johnyHV/SolderDispenser/FOTO/P_20200408_205617.jpg

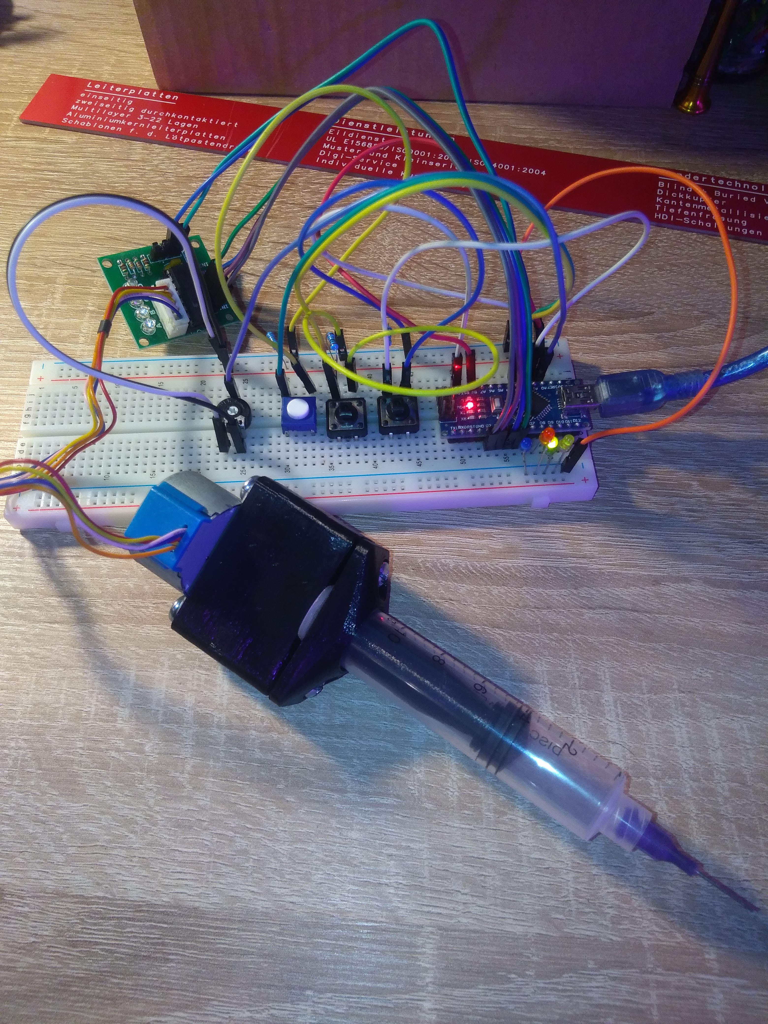
FOTO/P_20200408_205617.jpg
