johnyHV/SolderDispenser/FOTO/P_20200415_191209.jpg

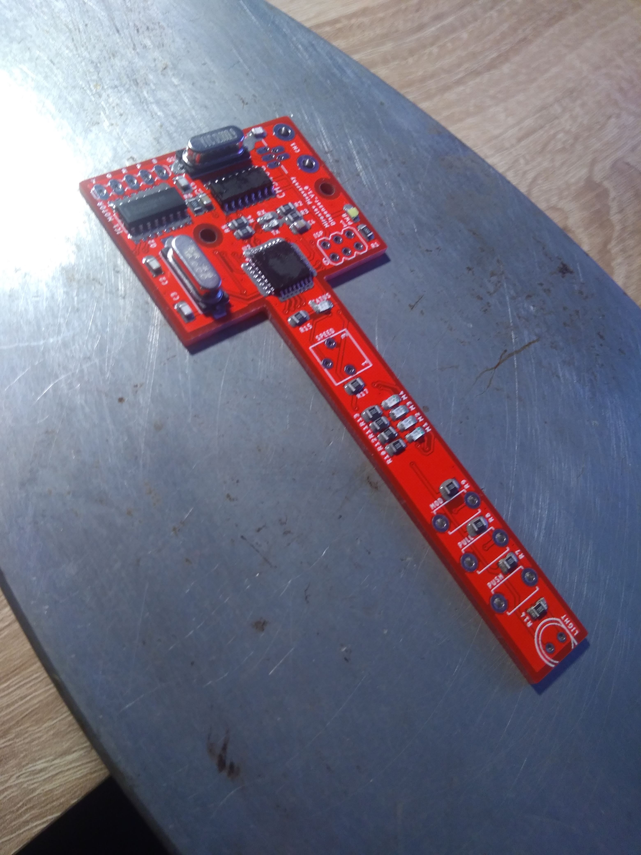
FOTO/P_20200415_191209.jpg
