johnyHV/SolderDispenser/FOTO/P_20200415_212830.jpg

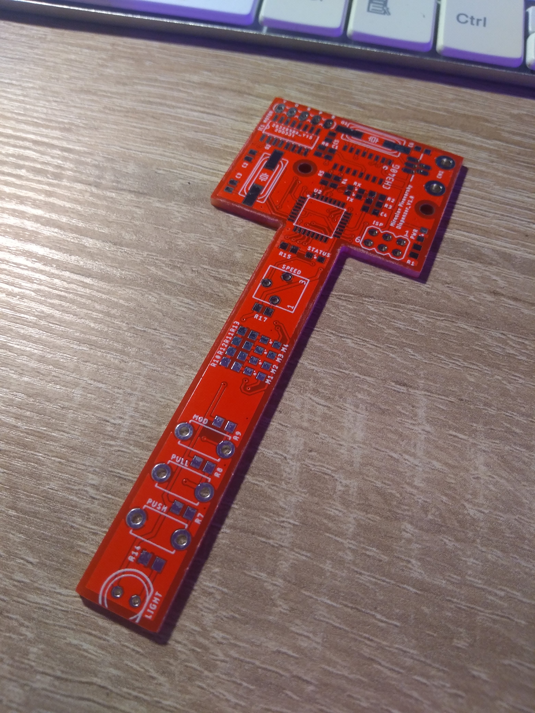
FOTO/P_20200415_212830.jpg
