johnyHV/SolderDispenser/FOTO/P_20200415_212847.jpg

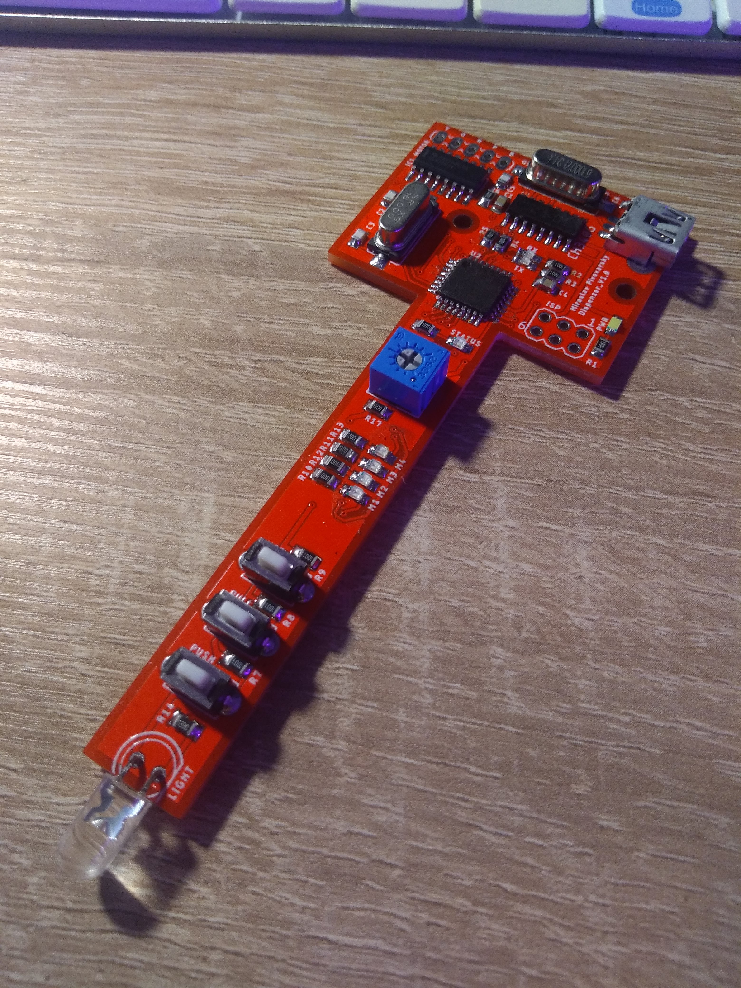
FOTO/P_20200415_212847.jpg
