johnyHV/SolderDispenser/FOTO/P_20200416_132119.jpg

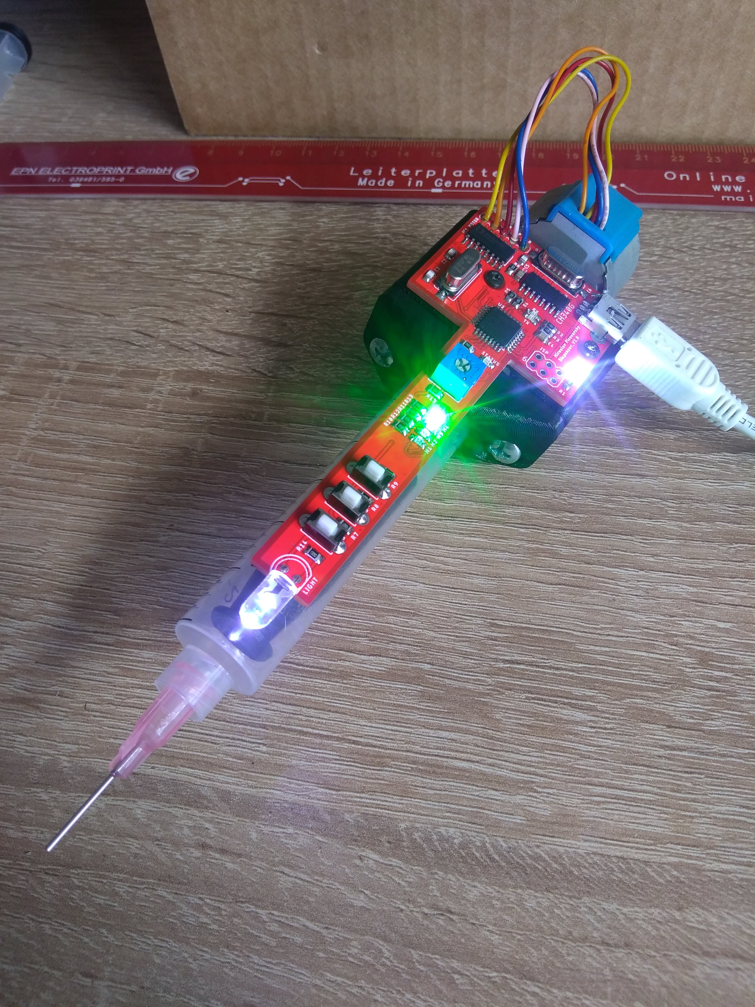
FOTO/P_20200416_132119.jpg
