johnyHV/SolderDispenser/FOTO/P_20200429_141248.jpg

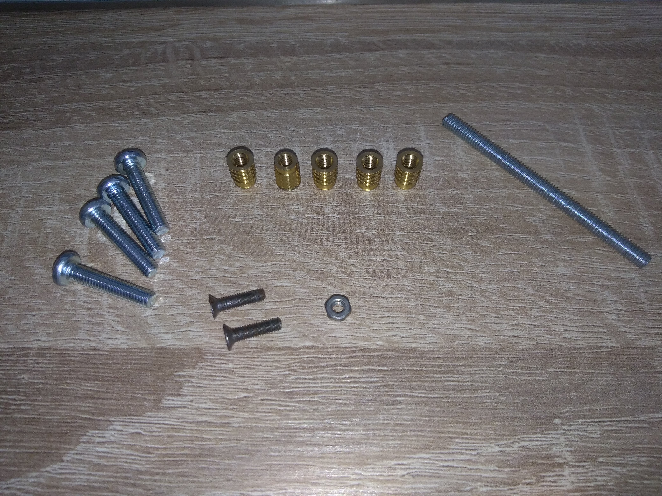
FOTO/P_20200429_141248.jpg
