johnyHV/SolderDispenser/FOTO/P_20200429_141258.jpg

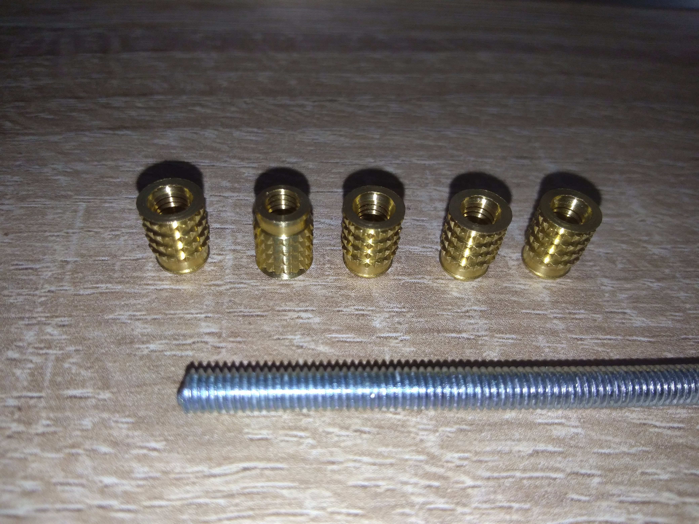
FOTO/P_20200429_141258.jpg
