johnyHV/SolderDispenser/FOTO/P_20200429_141528.jpg

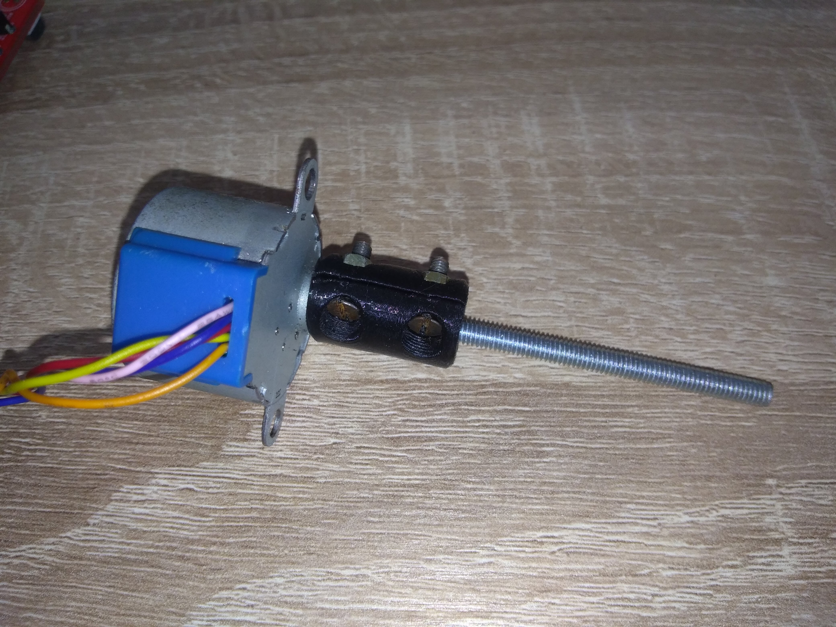
FOTO/P_20200429_141528.jpg
