johnyHV/SolderDispenser/FOTO/P_20200429_141551.jpg

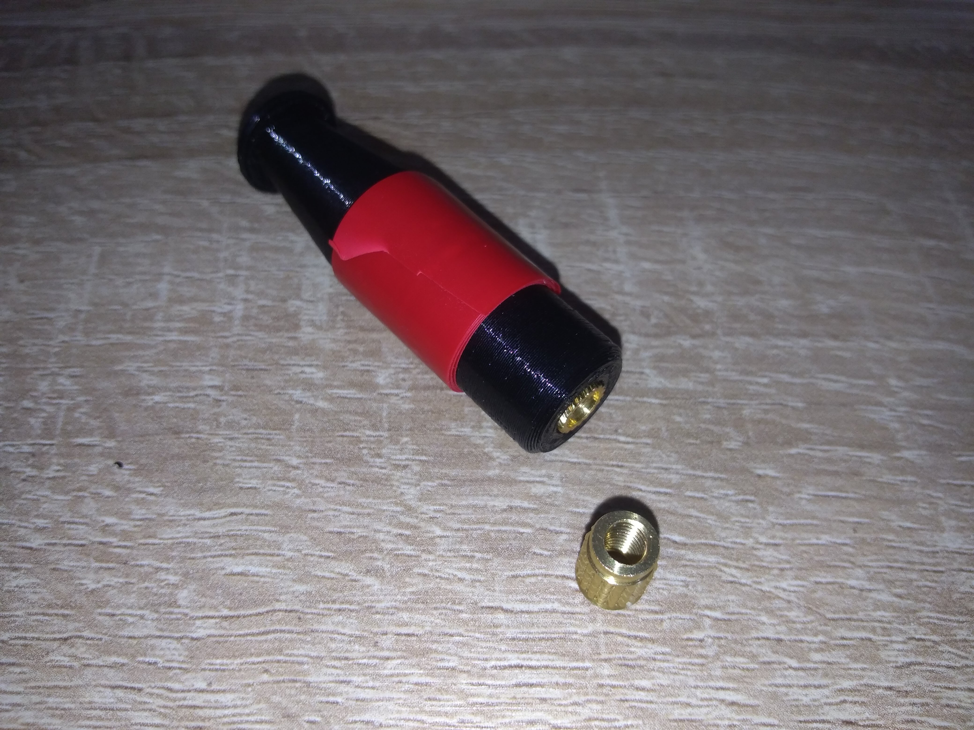
FOTO/P_20200429_141551.jpg
