johnyHV/SolderDispenser/FOTO/P_20200429_141635.jpg

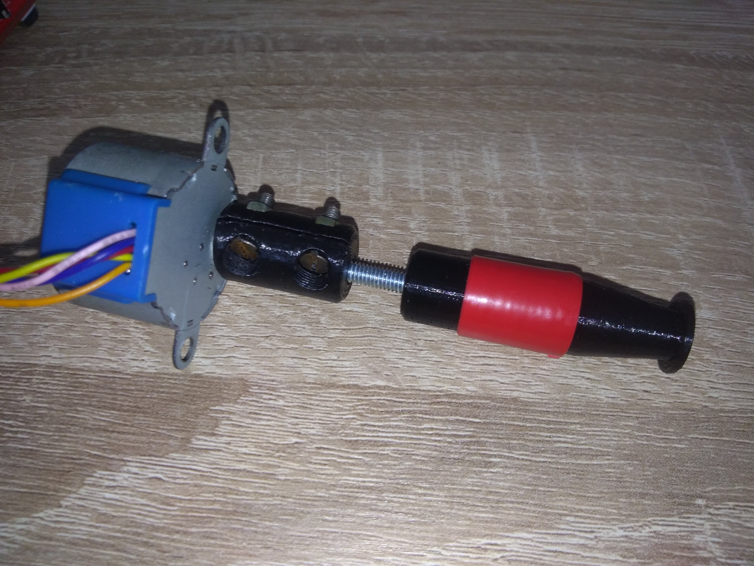
FOTO/P_20200429_141635.jpg
