johnyHV/SolderDispenser/FOTO/P_20200429_141740.jpg

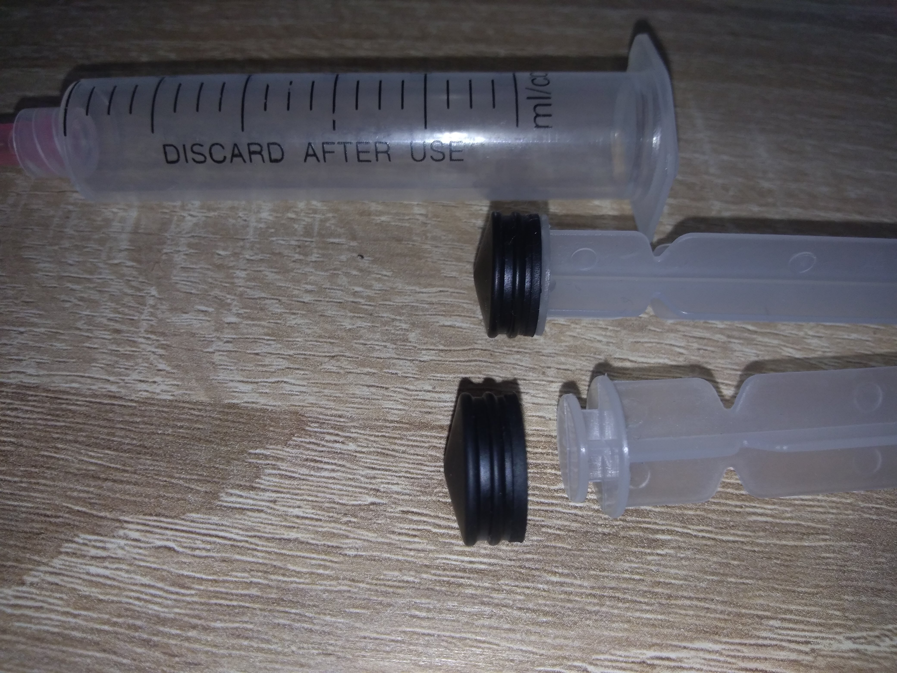
FOTO/P_20200429_141740.jpg
