johnyHV/SolderDispenser/FOTO/P_20200429_143029.jpg

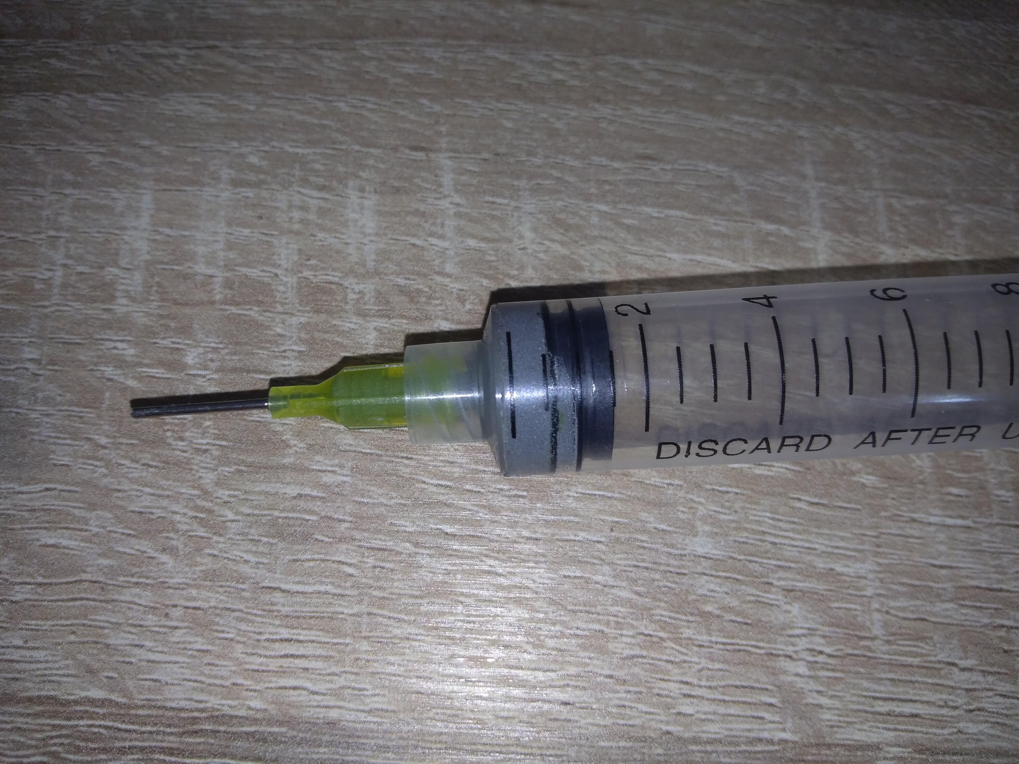
FOTO/P_20200429_143029.jpg
