johnyHV/SolderDispenser/FOTO/P_20200429_143421.jpg

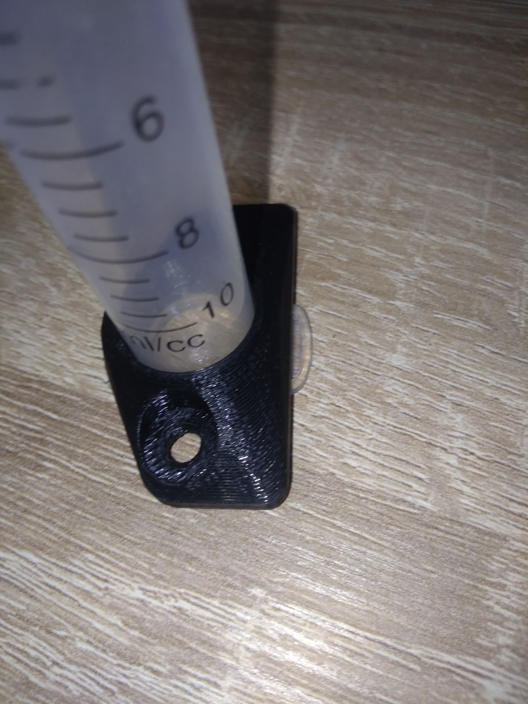
FOTO/P_20200429_143421.jpg
