johnyHV/SolderDispenser/FOTO/P_20200429_143431.jpg

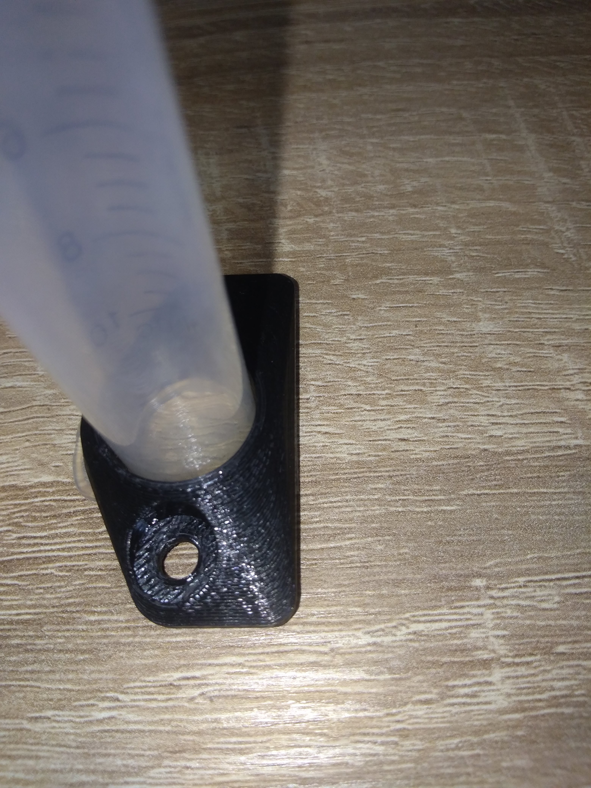
FOTO/P_20200429_143431.jpg
