johnyHV/SolderDispenser/FOTO/P_20200429_144857.jpg

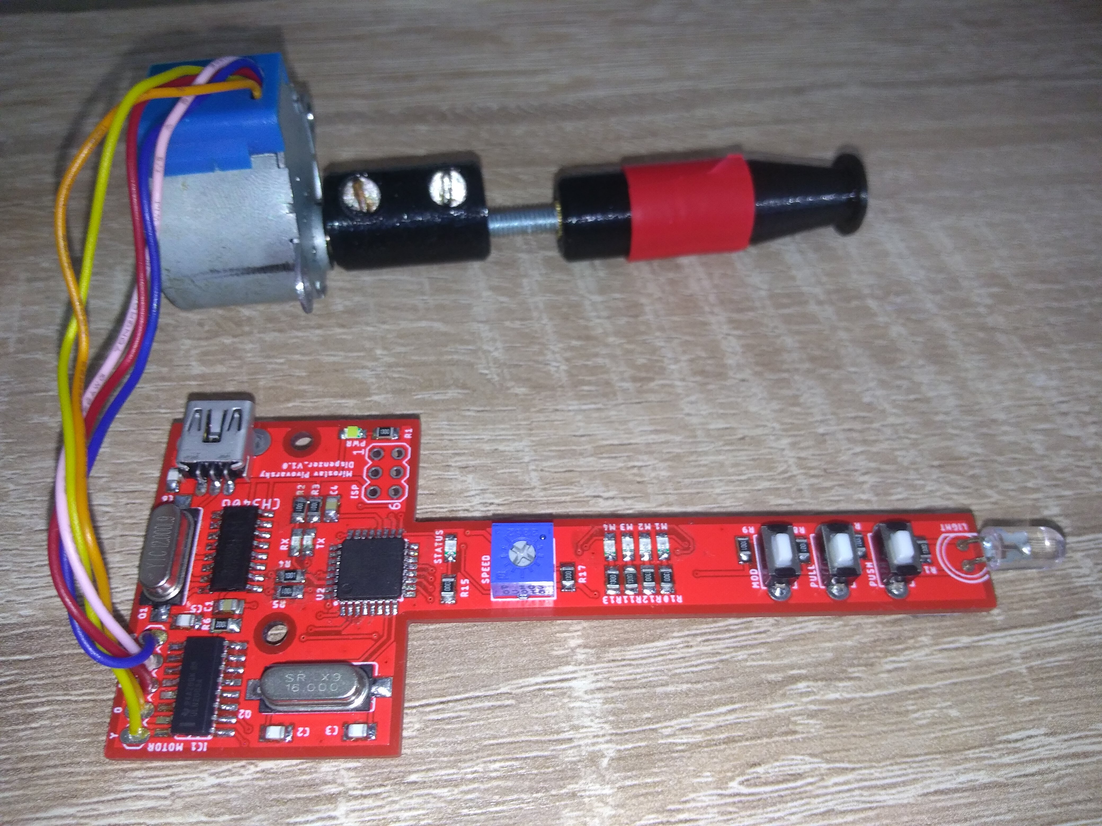
FOTO/P_20200429_144857.jpg
