johnyHV/SolderDispenser/FOTO/P_20200429_144904.jpg

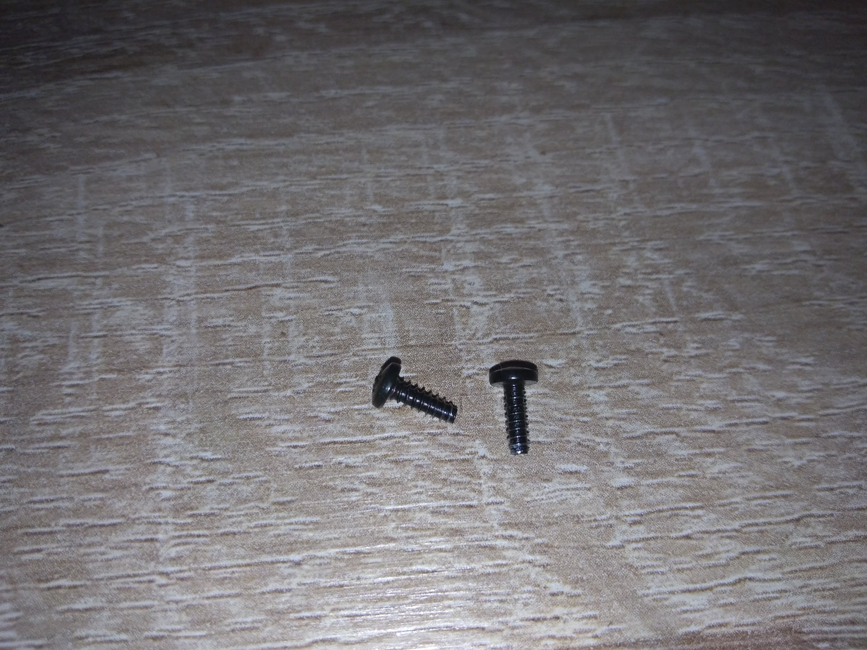
FOTO/P_20200429_144904.jpg
