johnyHV/SolderDispenser/FOTO/P_20200430_154544.jpg

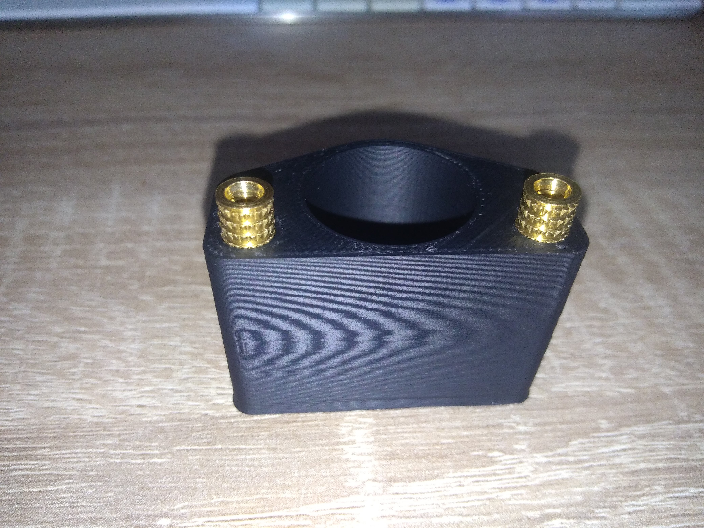
FOTO/P_20200430_154544.jpg
