johnyHV/SolderDispenser/FOTO/P_20200430_170257.jpg

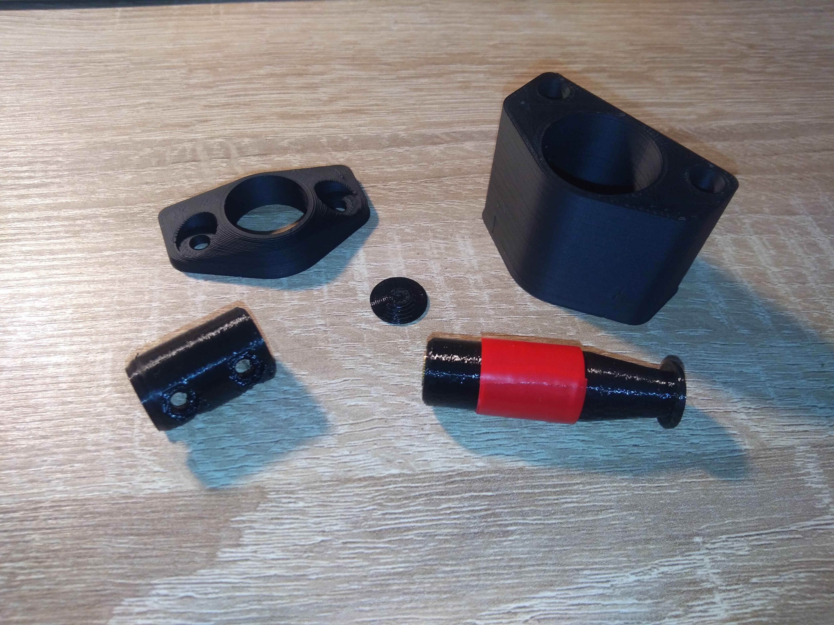
FOTO/P_20200430_170257.jpg
