johnyHV/SolderDispenser/FOTO/P_20200430_170945.jpg

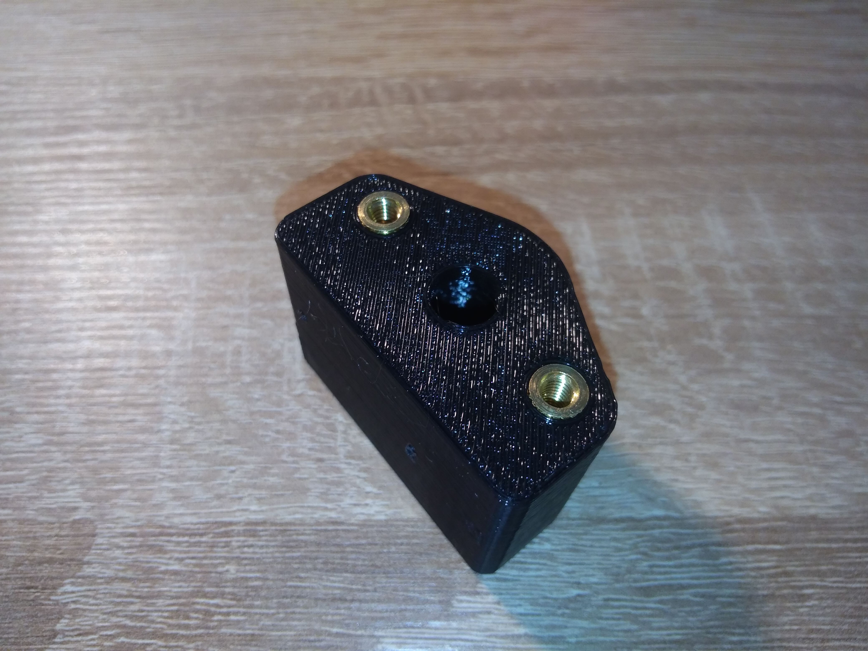
FOTO/P_20200430_170945.jpg
