johnyHV/SolderDispenser/FOTO/P_20200430_172939.jpg

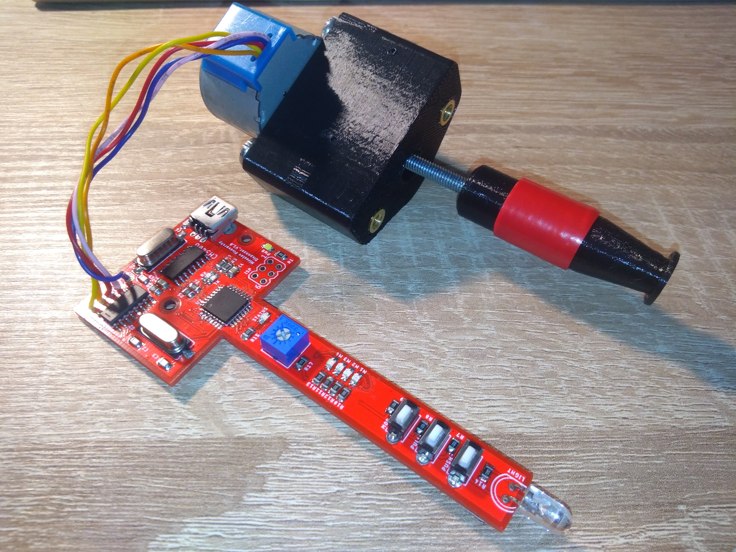
FOTO/P_20200430_172939.jpg
