johnyHV/SolderDispenser/FOTO/P_20200430_174215.jpg

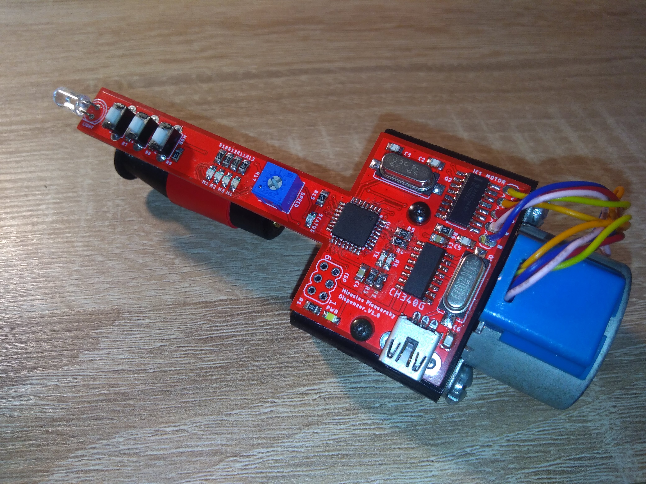
FOTO/P_20200430_174215.jpg
